Timothe-Renaud/SplitKeeb/ERGOOOO/ErgoDone/pro_micro_teensy_2.0_comparsion.png

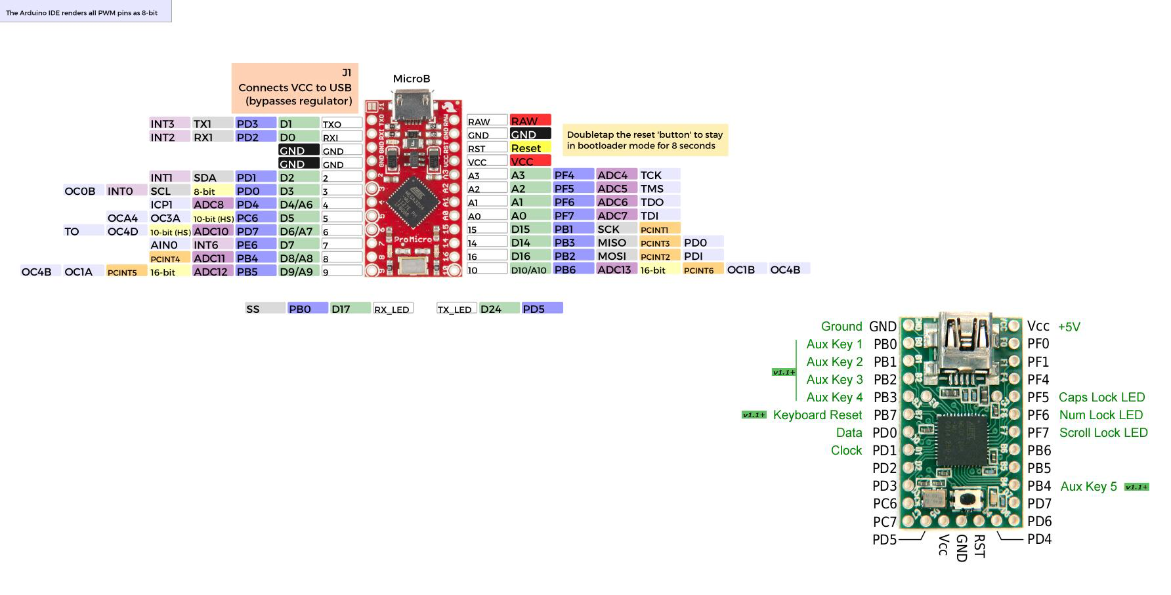
ERGOOOO/ErgoDone/pro_micro_teensy_2.0_comparsion.png
