Timothe-Renaud/SplitKeeb/OtherTypeOf Keyboard/SOFLE/Design/v2/Comparison1_2.png

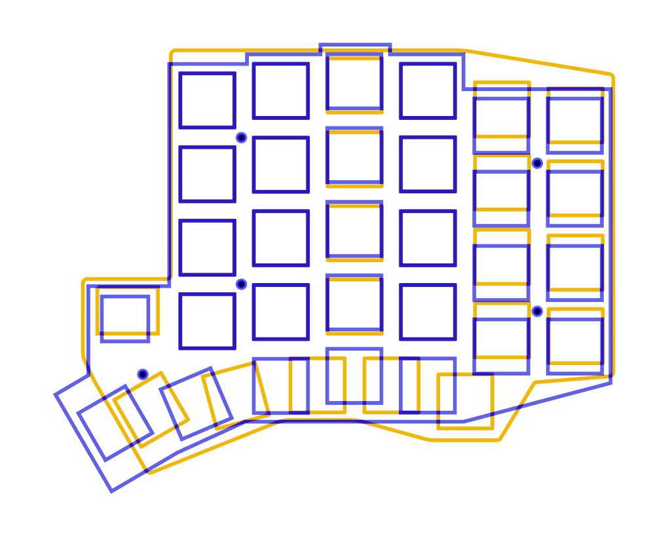
OtherTypeOf Keyboard/SOFLE/Design/v2/Comparison1_2.png
