Timothe-Renaud/SplitKeeb/OtherTypeOf Keyboard/SOFLE/docs/images/IMG_20191104_202757.jpg

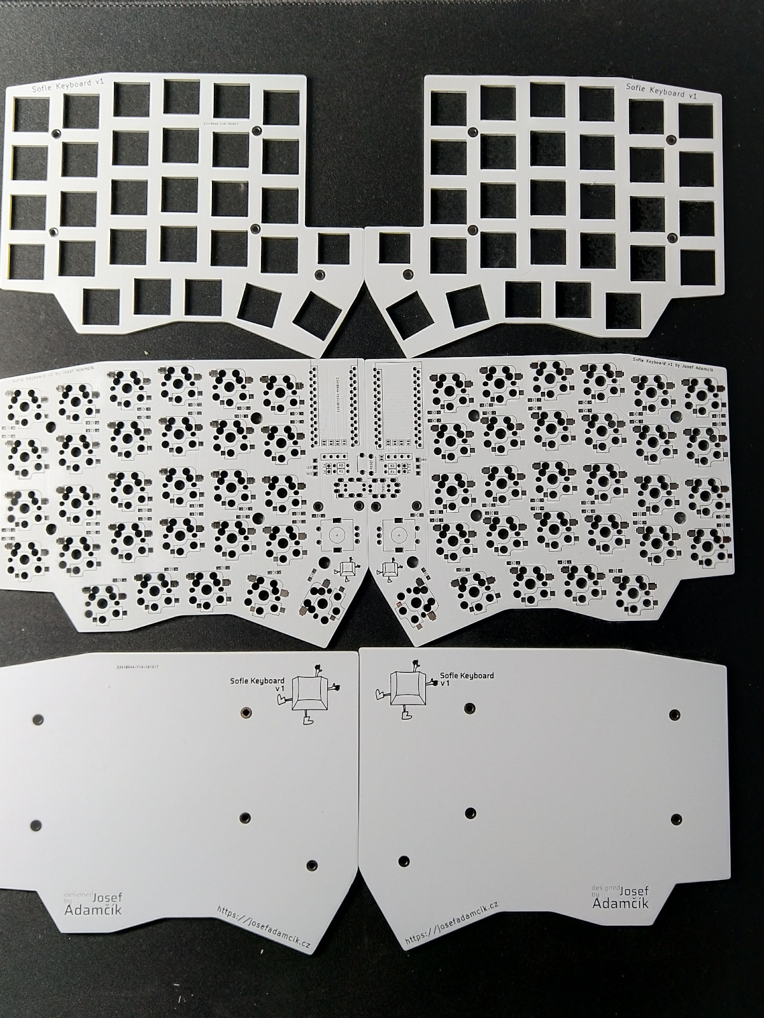
OtherTypeOf Keyboard/SOFLE/docs/images/IMG_20191104_202757.jpg
