Timothe-Renaud/SplitKeeb/OtherTypeOf Keyboard/SOFLE/docs/images/IMG_20191110_131443.jpg

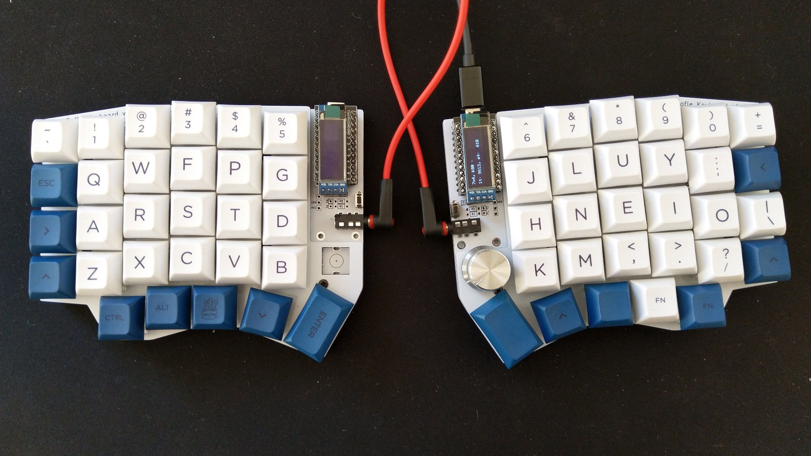
OtherTypeOf Keyboard/SOFLE/docs/images/IMG_20191110_131443.jpg
