Timothe-Renaud/SplitKeeb/OtherTypeOf Keyboard/SOFLE/docs/images/IMG_20200126_114622.jpg

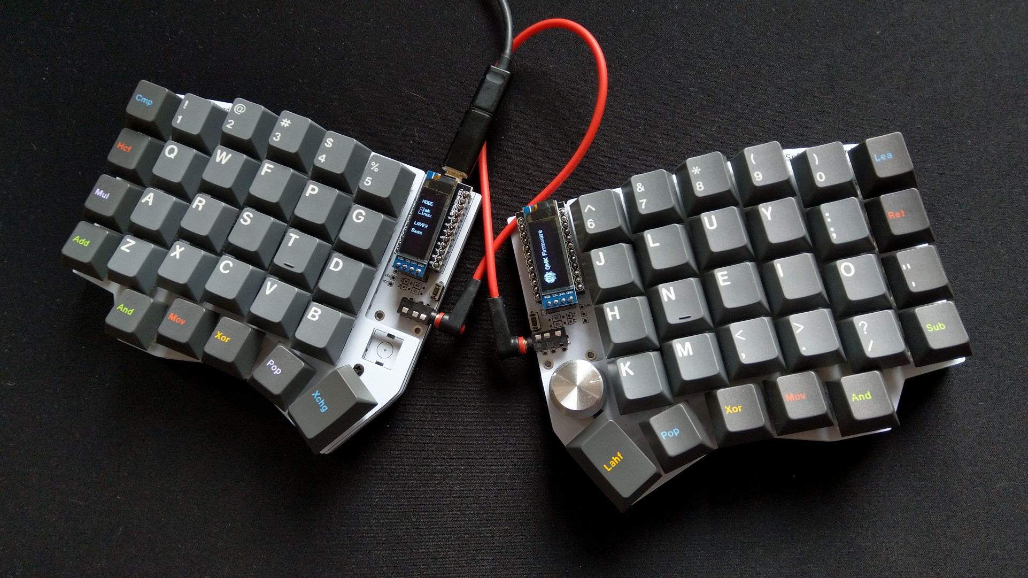
OtherTypeOf Keyboard/SOFLE/docs/images/IMG_20200126_114622.jpg
