Timothe-Renaud/SplitKeeb/OtherTypeOf Keyboard/SOFLE/docs/images/IMG_20200522_190925.jpg

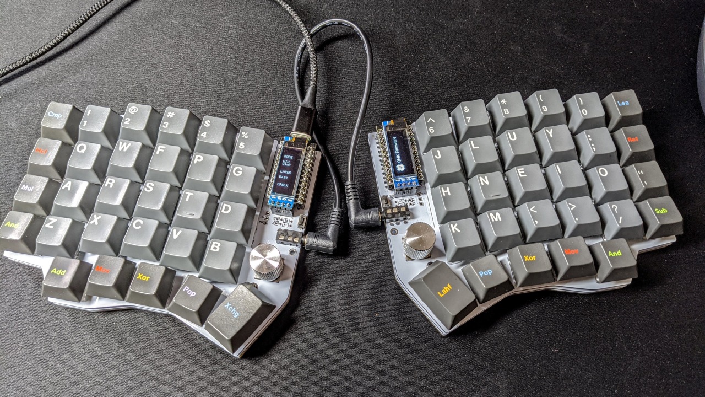
OtherTypeOf Keyboard/SOFLE/docs/images/IMG_20200522_190925.jpg
