Timothe-Renaud/SplitKeeb/OtherTypeOf Keyboard/SOFLE/docs/images/IMG_20200613_150327.jpg

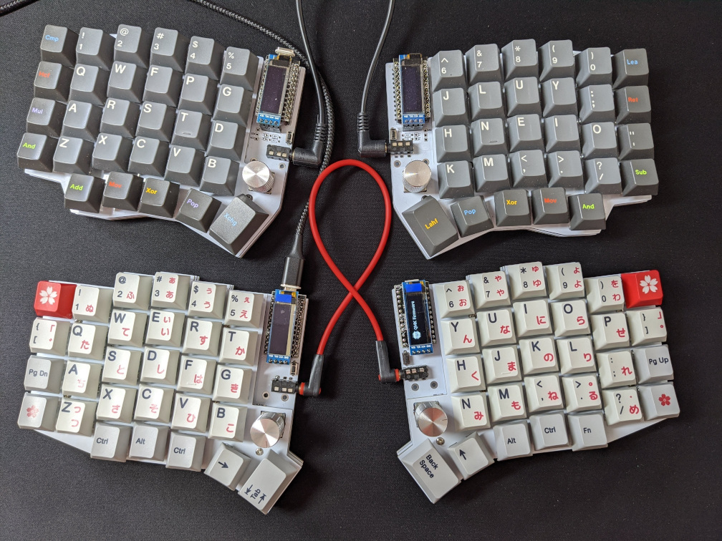
OtherTypeOf Keyboard/SOFLE/docs/images/IMG_20200613_150327.jpg
