Timothe-Renaud/SplitKeeb/OtherTypeOf Keyboard/SOFLE/docs/images/PXL_20200918_175110300.jpg

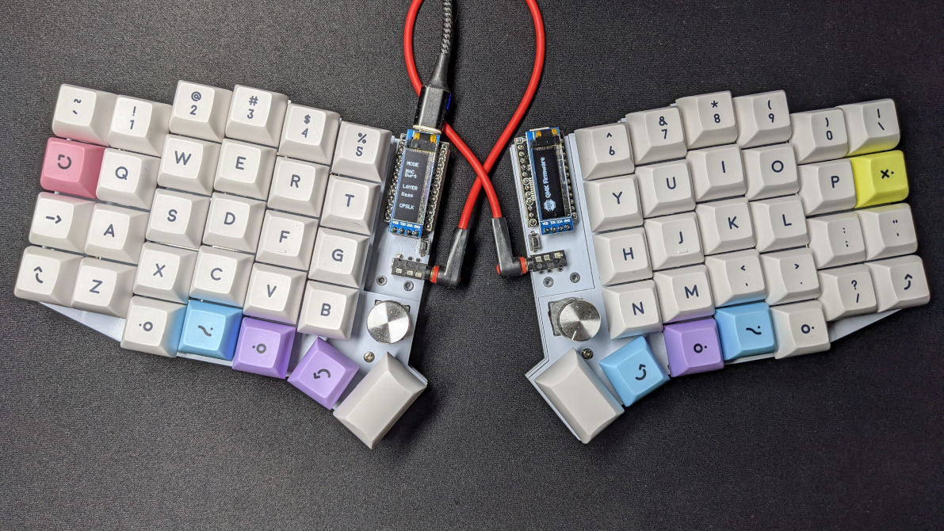
OtherTypeOf Keyboard/SOFLE/docs/images/PXL_20200918_175110300.jpg
