Timothe-Renaud/SplitKeeb/OtherTypeOf Keyboard/SOFLE/docs/images/render_pcb.png

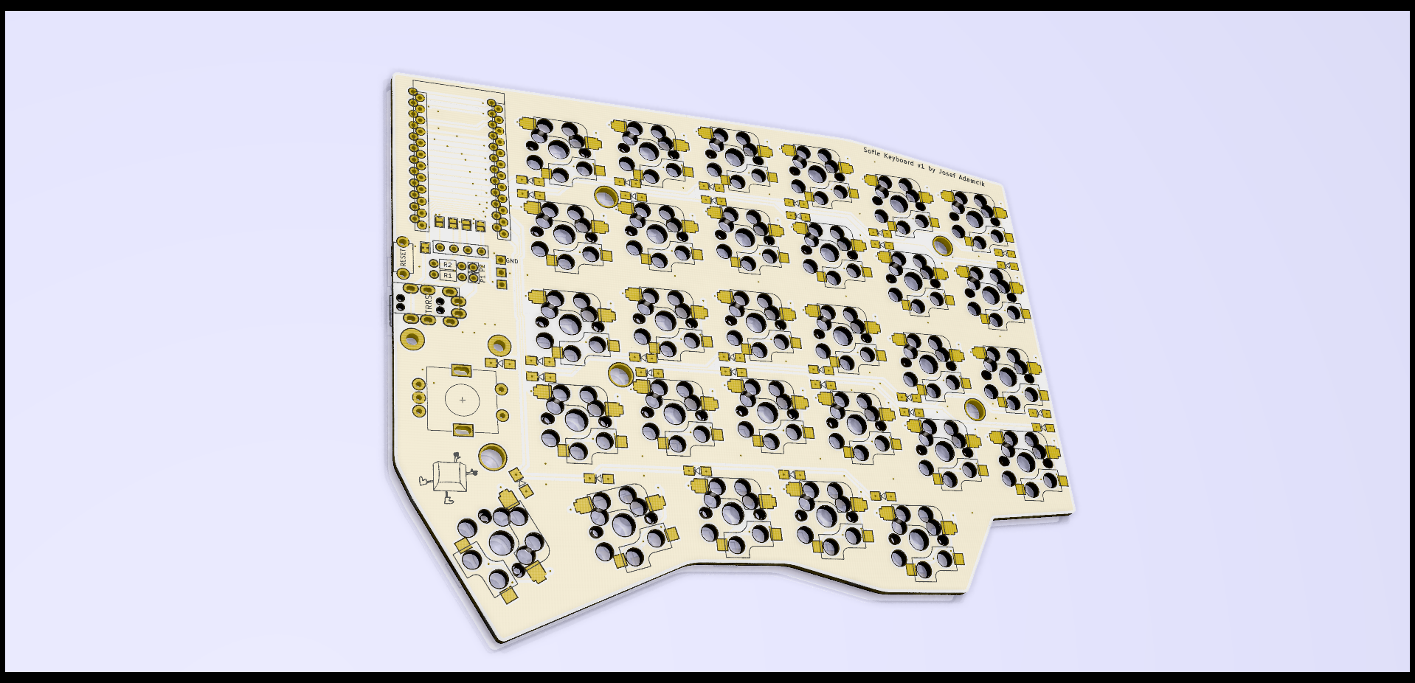
OtherTypeOf Keyboard/SOFLE/docs/images/render_pcb.png
