Timothe-Renaud/SplitKeeb/OtherTypeOf Keyboard/SOFLE/docs/images/socketing2.jpg

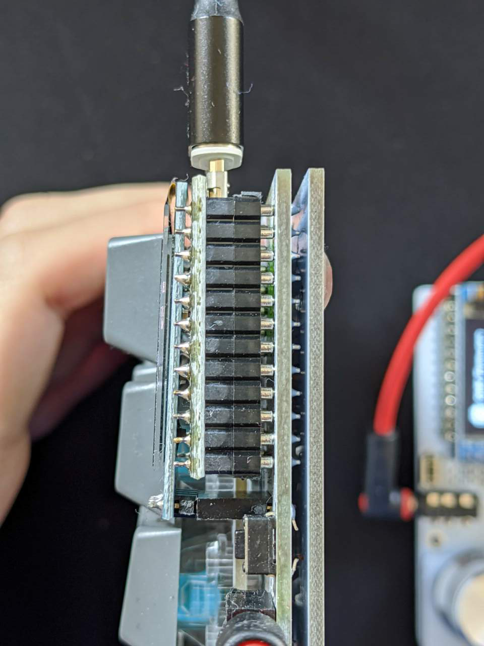
OtherTypeOf Keyboard/SOFLE/docs/images/socketing2.jpg
