Timothe-Renaud/SplitKeeb/OtherTypeOf Keyboard/SOFLE/docs/images/socketing.jpg

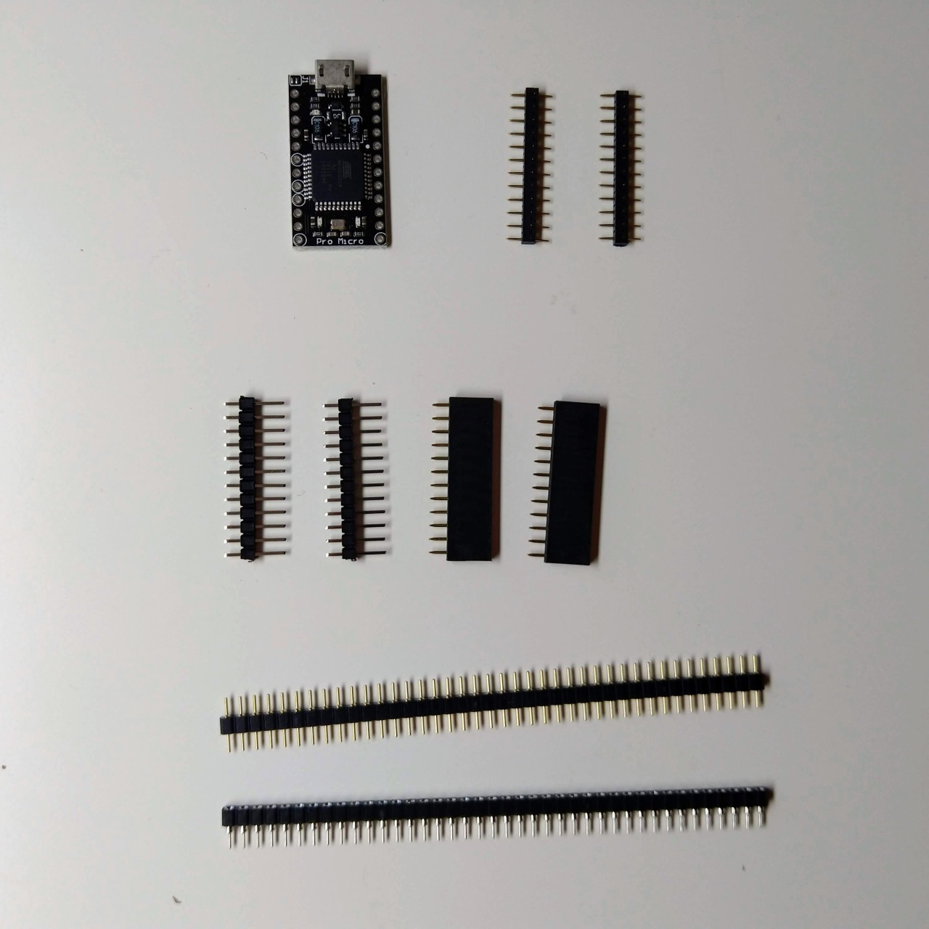
OtherTypeOf Keyboard/SOFLE/docs/images/socketing.jpg
