Timothe-Renaud/SplitKeeb/OtherTypeOf Keyboard/SOFLE/docs/images/sofle_choc.jpg

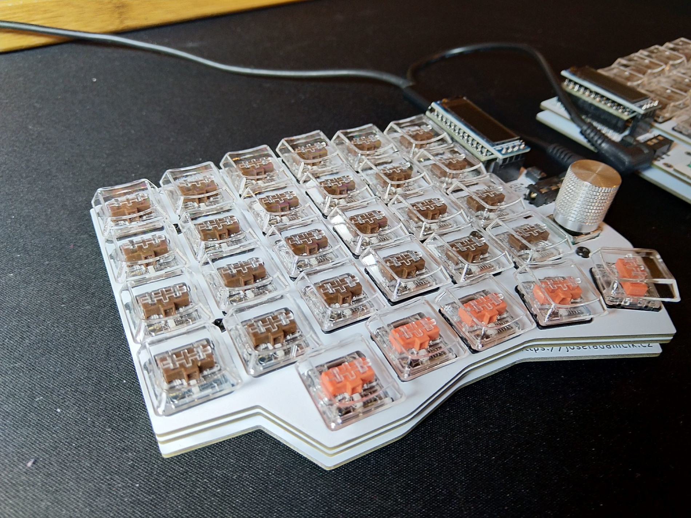
OtherTypeOf Keyboard/SOFLE/docs/images/sofle_choc.jpg
