Timothe-Renaud/SplitKeeb/OtherTypeOf Keyboard/SOFLE/docs/images/soflekeyboard_layout_adjust.png

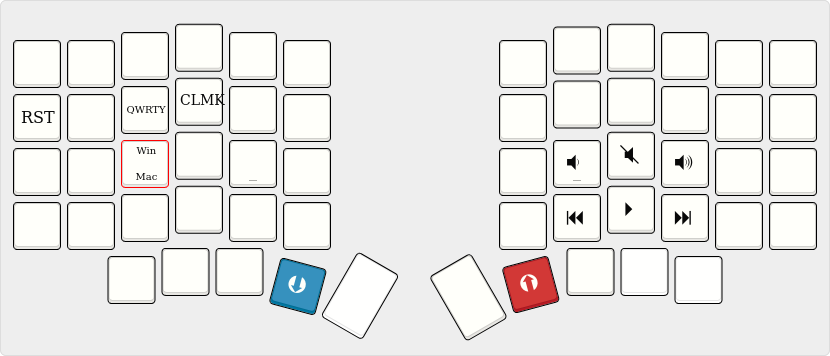
OtherTypeOf Keyboard/SOFLE/docs/images/soflekeyboard_layout_adjust.png
