Timothe-Renaud/SplitKeeb/OtherTypeOf Keyboard/SOFLE/docs/images/SofleKeyboardBottomPlate.png

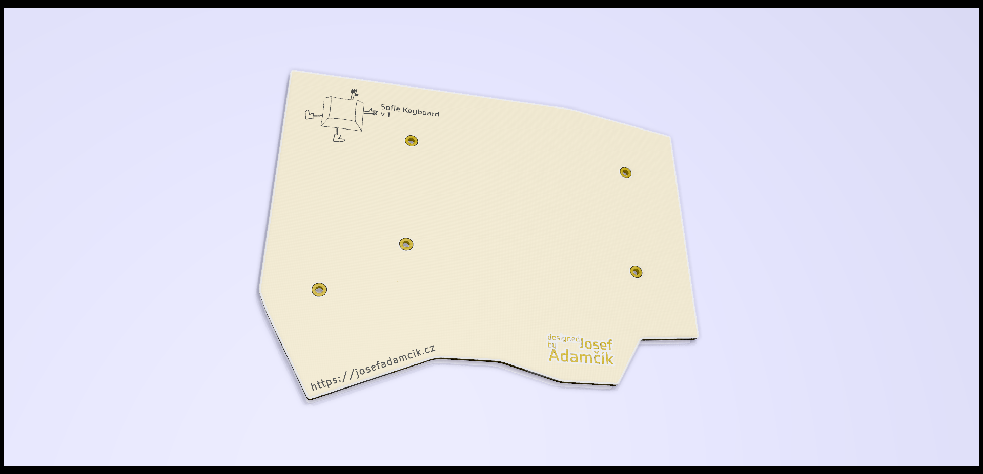
OtherTypeOf Keyboard/SOFLE/docs/images/SofleKeyboardBottomPlate.png
