Timothe-Renaud/SplitKeeb/OtherTypeOf Keyboard/SOFLE/docs/images/SofleKeyboardTopPlate.png

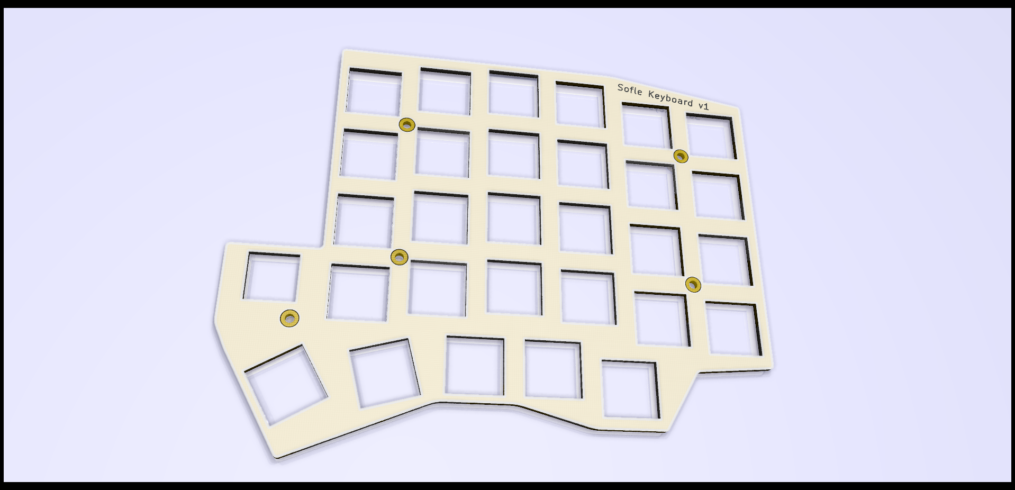
OtherTypeOf Keyboard/SOFLE/docs/images/SofleKeyboardTopPlate.png
