Timothe-Renaud/SplitKeeb/OtherTypeOf Keyboard/SOFLE/Images/chocclear.jpg

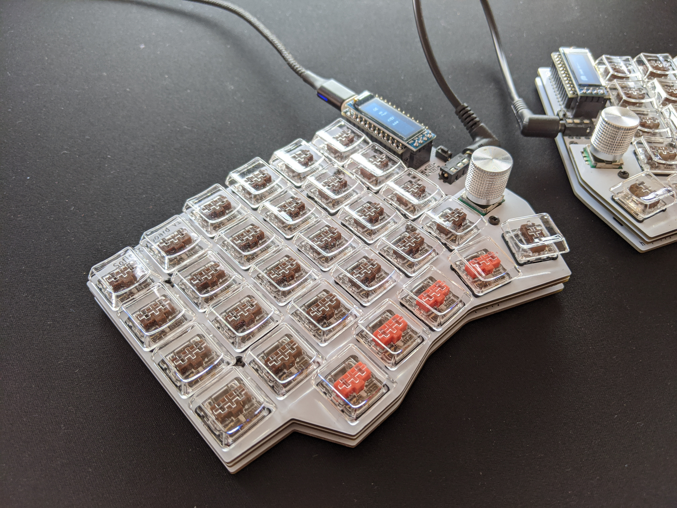
OtherTypeOf Keyboard/SOFLE/Images/chocclear.jpg
