Timothe-Renaud/SplitKeeb/OtherTypeOf Keyboard/SOFLE/Images/SofleKeyboard2-freecad.png

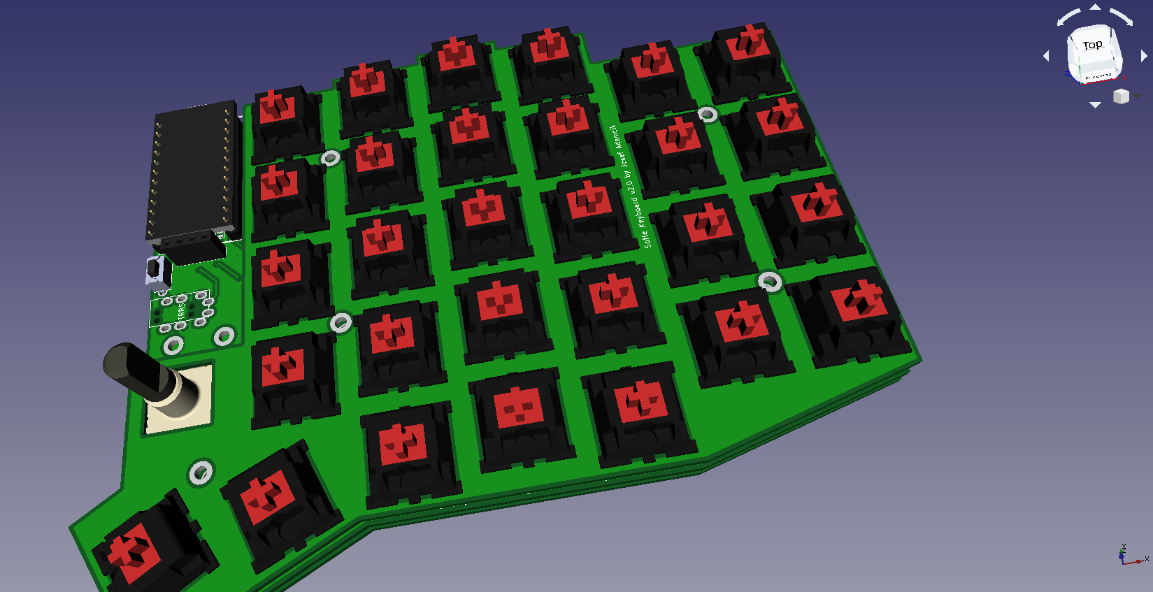
OtherTypeOf Keyboard/SOFLE/Images/SofleKeyboard2-freecad.png
