Timothe-Renaud/SplitKeeb/OtherTypeOf Keyboard/SOFLE/Images/SofleKeyboard2_bottom_plate_render.jpg

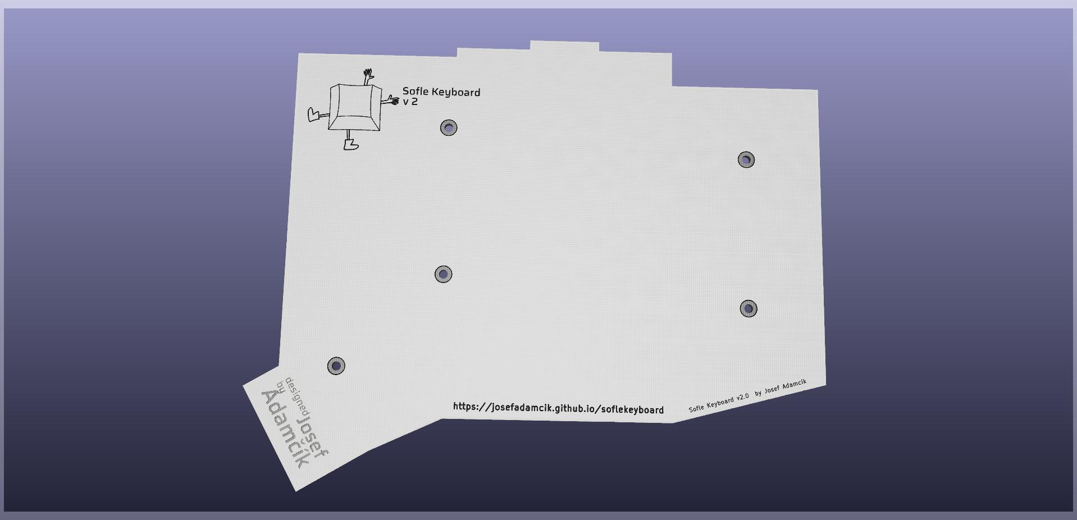
OtherTypeOf Keyboard/SOFLE/Images/SofleKeyboard2_bottom_plate_render.jpg
