Timothe-Renaud/SplitKeeb/OtherTypeOf Keyboard/SOFLE/Images/SofleKeyboard2_render1.jpg

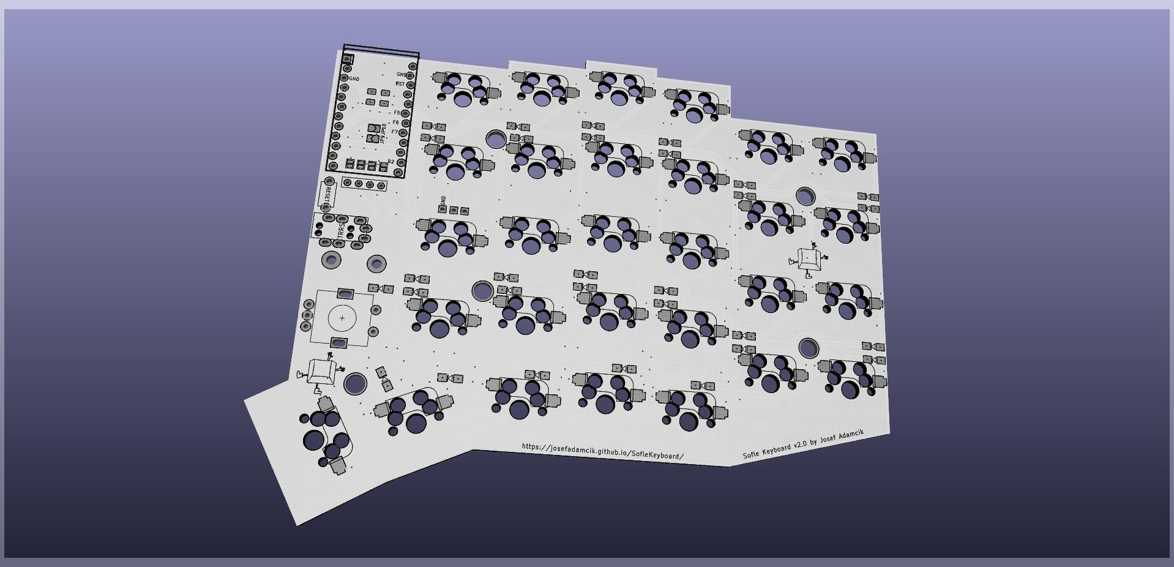
OtherTypeOf Keyboard/SOFLE/Images/SofleKeyboard2_render1.jpg
