Timothe-Renaud/SplitKeeb/OtherTypeOf Keyboard/SOFLE/Images/SofleKeyboard2_render2.jpg

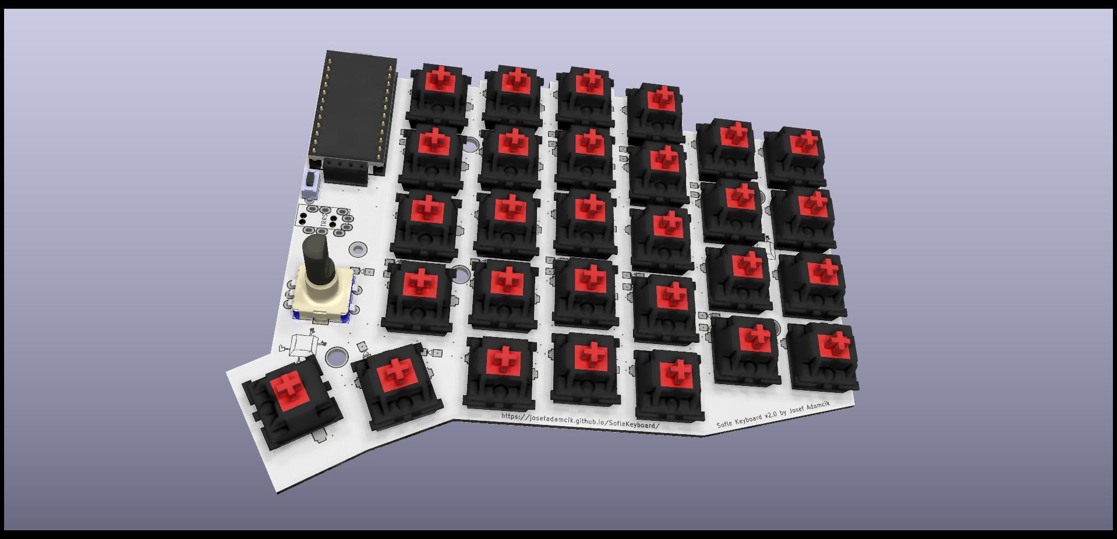
OtherTypeOf Keyboard/SOFLE/Images/SofleKeyboard2_render2.jpg
