Timothe-Renaud/SplitKeeb/OtherTypeOf Keyboard/SOFLE/Images/SofleKeyboard2_render3.jpg

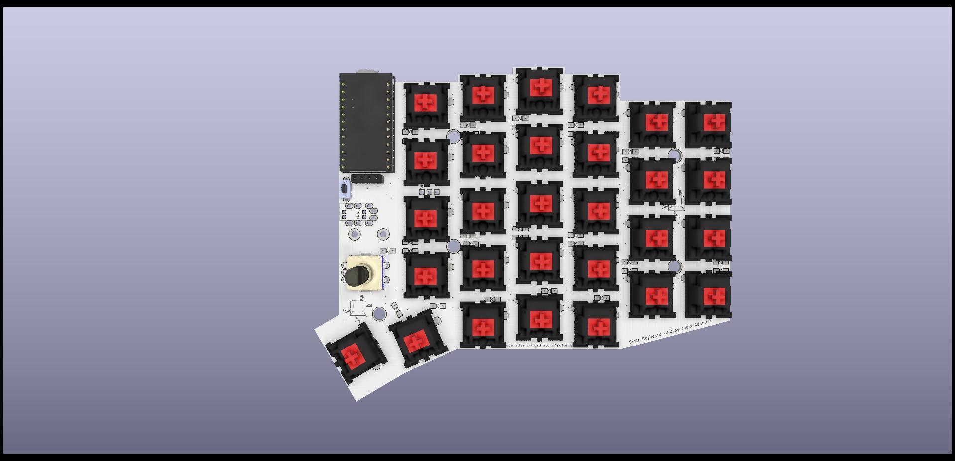
OtherTypeOf Keyboard/SOFLE/Images/SofleKeyboard2_render3.jpg
