Timothe-Renaud/SplitKeeb/OtherTypeOf Keyboard/SOFLE/Images/SofleKeyboard2_render4.jpg

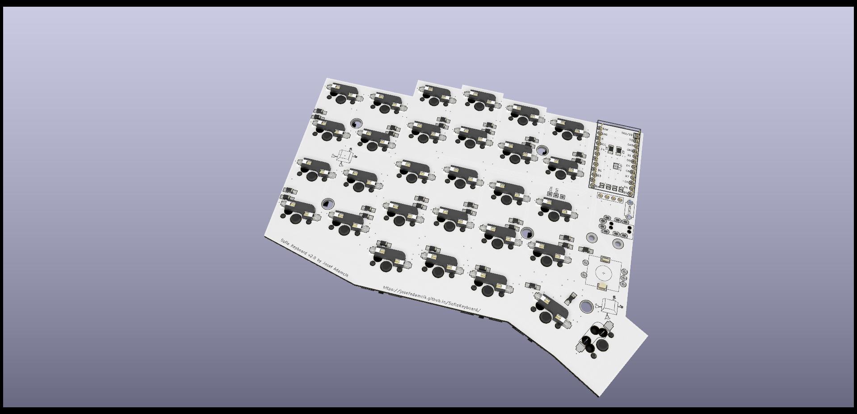
OtherTypeOf Keyboard/SOFLE/Images/SofleKeyboard2_render4.jpg
