Timothe-Renaud/SplitKeeb/OtherTypeOf Keyboard/SOFLE/Images/SofleKeyboard2_top_plate_render.jpg

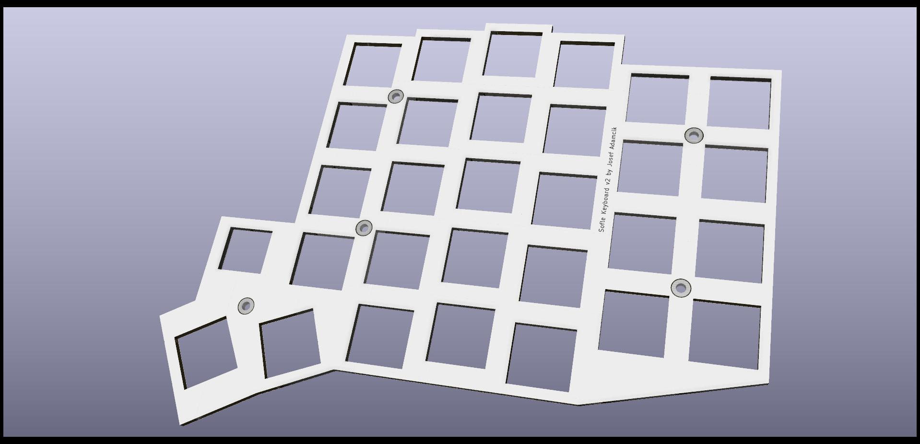
OtherTypeOf Keyboard/SOFLE/Images/SofleKeyboard2_top_plate_render.jpg
