Timothe-Renaud/SplitKeeb/ERGOOOO/ErgoDox/ErgoDox Acrylic Case/ErgoDOX Acrylic Case - Designed by Litster/Standard/Right/ErgoDOX Case Layer 1 Top - Right.dxf

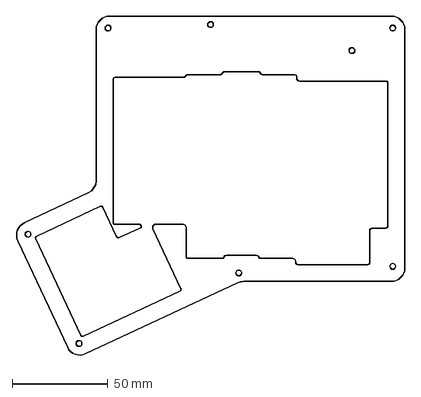
[picture p38: CAD file, 2022-05-24]
ERGOOOO/ErgoDox/ErgoDox Acrylic Case/ErgoDOX Acrylic Case - Designed by Litster/Standard/Right/ErgoDOX Case Layer 1 Top - Right.dxf
202.8 x 177.8 mm
