Timothe-Renaud/SplitKeeb/ERGOOOO/ErgoDox/ErgoDox Acrylic Case/ErgoDOX Acrylic Case - Designed by Litster/with Wrist Rest/Left/ErgoDOX Case Layer 2 Spacer - Left.dxf

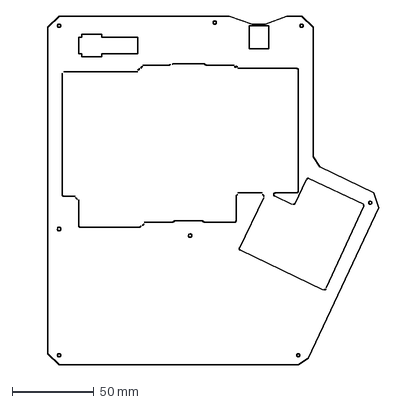
[picture p39: CAD file, 2022-05-24]
ERGOOOO/ErgoDox/ErgoDox Acrylic Case/ErgoDOX Acrylic Case - Designed by Litster/with Wrist Rest/Left/ErgoDOX Case Layer 2 Spacer - Left.dxf
221.0 x 213.0 mm
