Timothe-Renaud/SplitKeeb/ERGOOOO/ErgoDox/ErgoDox Acrylic Case/ErgoDOX Acrylic Case - Designed by Litster/with Wrist Rest/Right/ErgoDOX Wrist Rest Case Layer 4 Spacer - Right.dxf

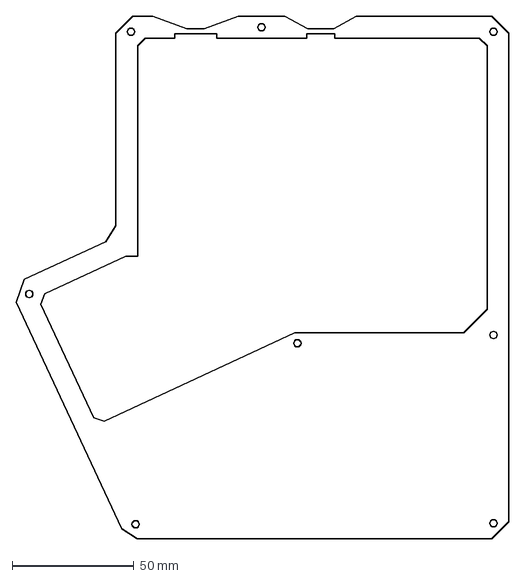
[picture p40: CAD file, 2022-05-24]
ERGOOOO/ErgoDox/ErgoDox Acrylic Case/ErgoDOX Acrylic Case - Designed by Litster/with Wrist Rest/Right/ErgoDOX Wrist Rest Case Layer 4 Spacer - Right.dxf
202.0 x 214.1 mm
