Timothe-Renaud/SplitKeeb/ERGOOOO/ErgoDox/ErgodoxCaseEcoMode/RightBottom.stl

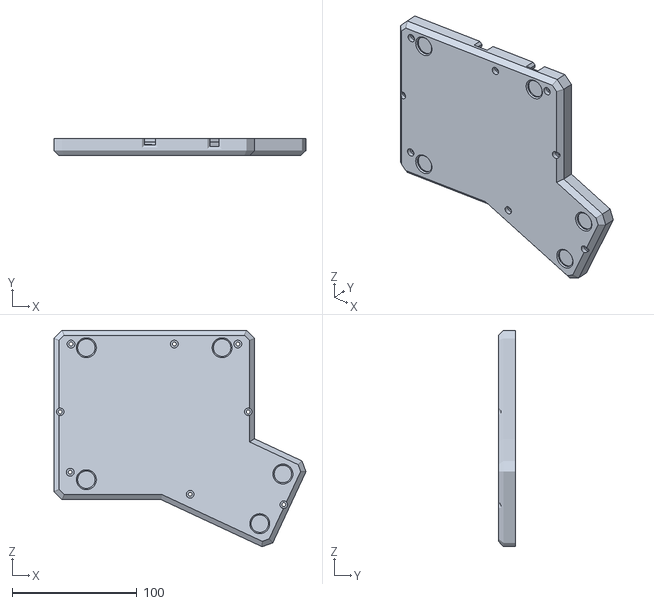
[picture p41: CAD file, 2022-05-24]
ERGOOOO/ErgoDox/ErgodoxCaseEcoMode/RightBottom.stl
202.4 x 13.7 x 173.8
