Timothe-Renaud/SplitKeeb/ERGOOOO/ErgoDone/CASE/ERGODOX CASE FULL 3D files/LeftPlate.stl

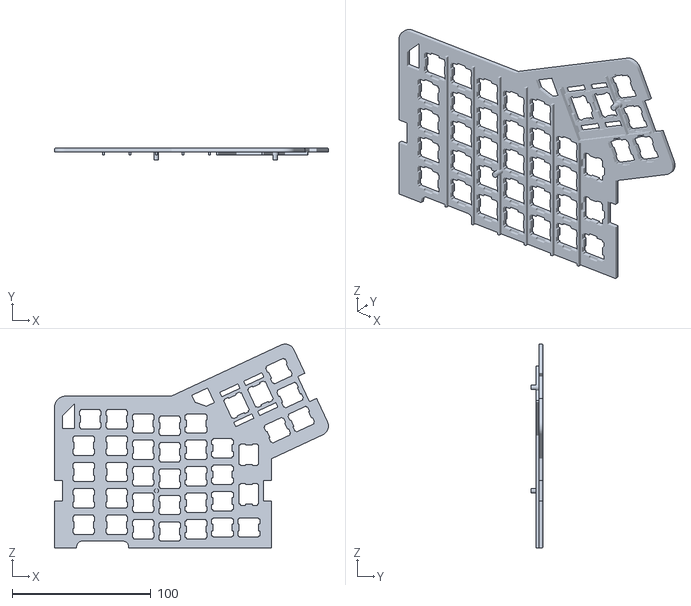
[picture p42: CAD file, 2022-05-24]
ERGOOOO/ErgoDone/CASE/ERGODOX CASE FULL 3D files/LeftPlate.stl
197.5 x 8.70 x 146.9
