Timothe-Renaud/SplitKeeb/ERGOOOO/ErgoDox/ErgoDox Acrylic Case/ErgoDOX Acrylic Case - Designed by Litster/Standard/Left/ErgoDOX Case Layer 5 Bottom - Left.dxf

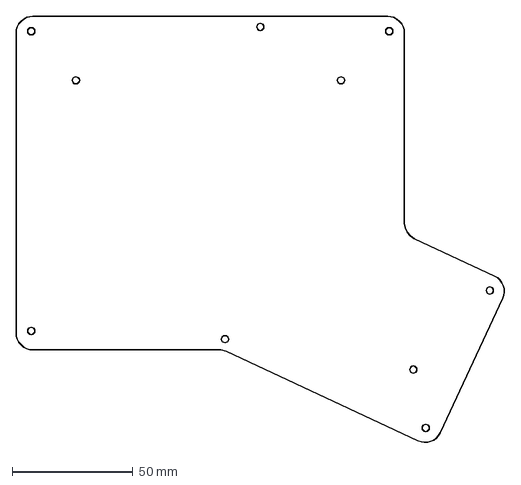
[picture p43: CAD file, 2022-05-24]
ERGOOOO/ErgoDox/ErgoDox Acrylic Case/ErgoDOX Acrylic Case - Designed by Litster/Standard/Left/ErgoDOX Case Layer 5 Bottom - Left.dxf
202.8 x 177.8 mm
