Timothe-Renaud/SplitKeeb/ERGOOOO/ErgoDox/ErgoDox Acrylic Case/ErgoDOX Acrylic Case - Designed by Litster/Standard/Right/ErgoDOX Case Layer 4 Spacer - Right.dxf

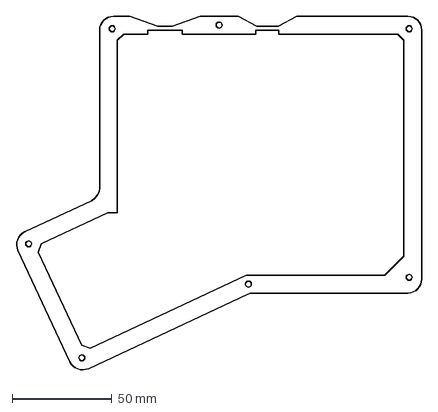
[picture p44: CAD file, 2022-05-24]
ERGOOOO/ErgoDox/ErgoDox Acrylic Case/ErgoDOX Acrylic Case - Designed by Litster/Standard/Right/ErgoDOX Case Layer 4 Spacer - Right.dxf
202.8 x 177.8 mm
