Timothe-Renaud/SplitKeeb/OtherTypeOf Keyboard/SOFLE/docs/images/build_guide/IMG_20191106_211037.jpg

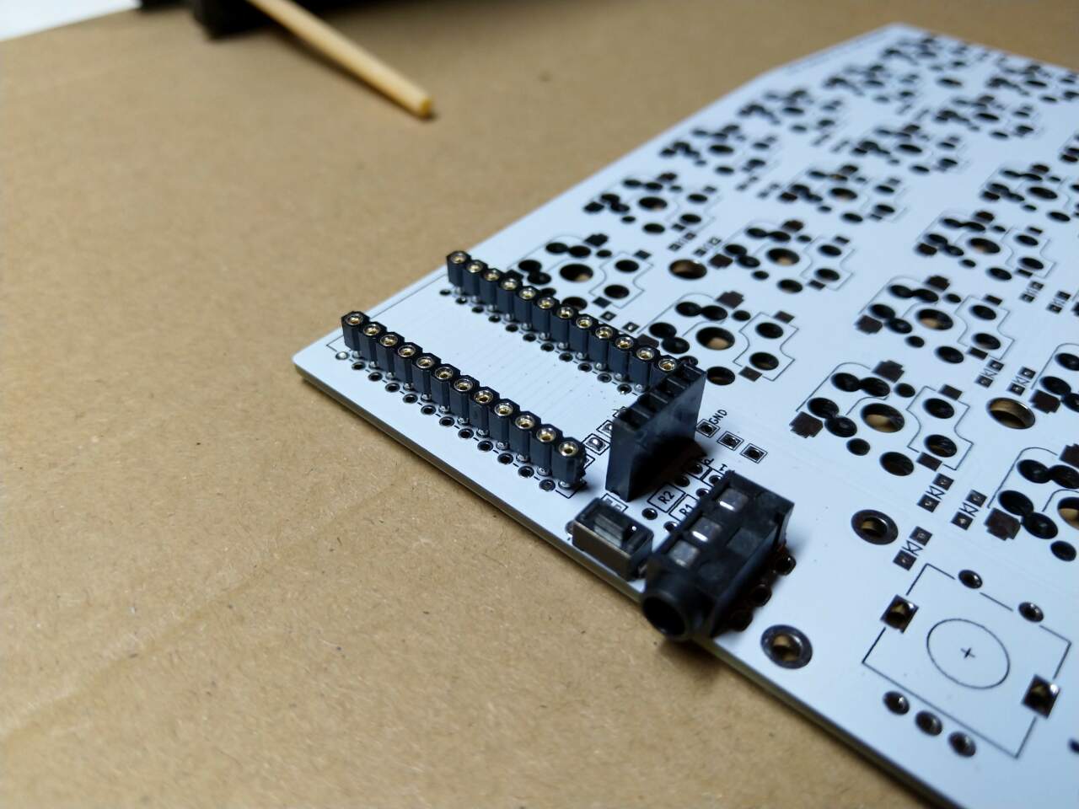
OtherTypeOf Keyboard/SOFLE/docs/images/build_guide/IMG_20191106_211037.jpg
