Timothe-Renaud/SplitKeeb/OtherTypeOf Keyboard/SOFLE/docs/images/build_guide/micro_placement_v1.jpg

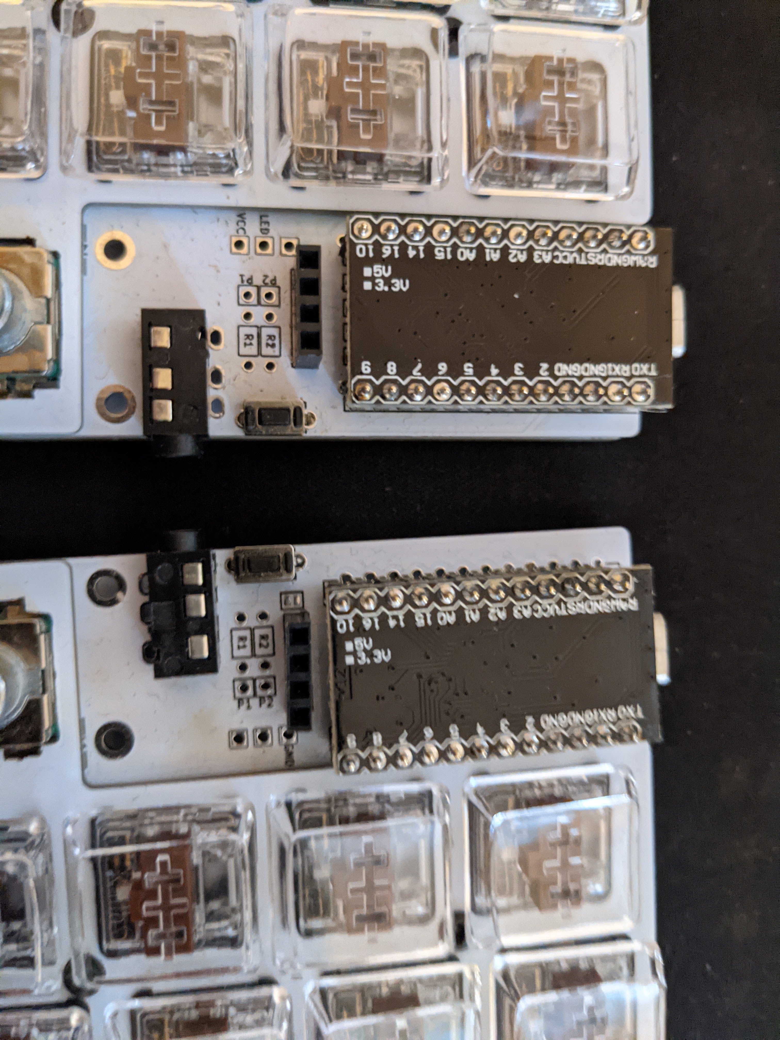
OtherTypeOf Keyboard/SOFLE/docs/images/build_guide/micro_placement_v1.jpg
