Timothe-Renaud/SplitKeeb/OtherTypeOf Keyboard/SOFLE/docs/images/build_guide_rgb/perkey lighting.png

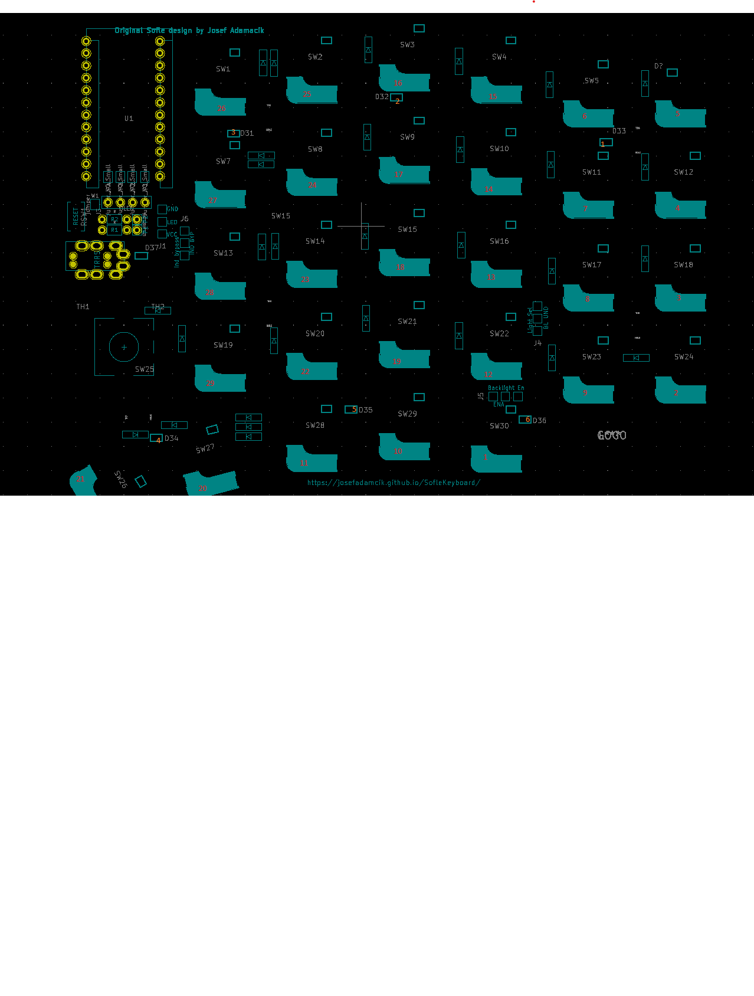
OtherTypeOf Keyboard/SOFLE/docs/images/build_guide_rgb/perkey lighting.png
